ArthorH/ModuCard-OrangePie/Simulation/Improved_delay.asc

C1: cap; 20µF; Rser=1
M1: nmos; AO6408
M2: pmos; AO6407
M3: pmos; AO6407
R1: res; 100k
R2: res; 100k
R3: res; 100k
R4: res; 100k
R5: res; 10k
R6: res; 100k
R7: res; 10k
R9: res; 10
RL: res; 1k
U1: SCR; MCR100-003
V1: voltage; PULSE(0 5 10 1u 1u 5 10 5)
Named nets: 0
.tran 100s
.lib MCR100-0003.sub
.inc AO3400.mod
.inc AO3401A.mod
